julienrat/wemostowio/3D/wio_shield.png

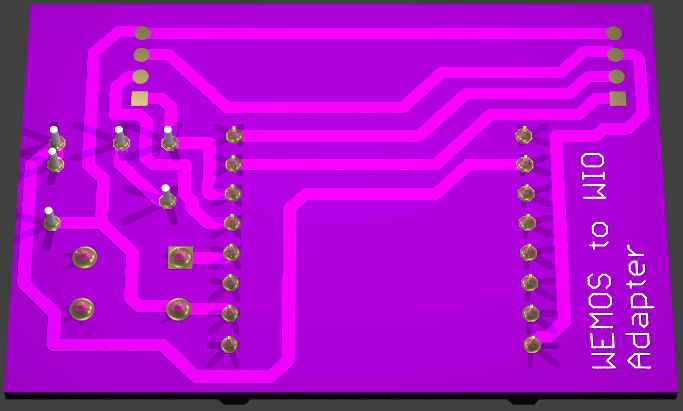
3D/wio_shield.png
