julienrat/wemostowio/3D/wio_shield_top.png

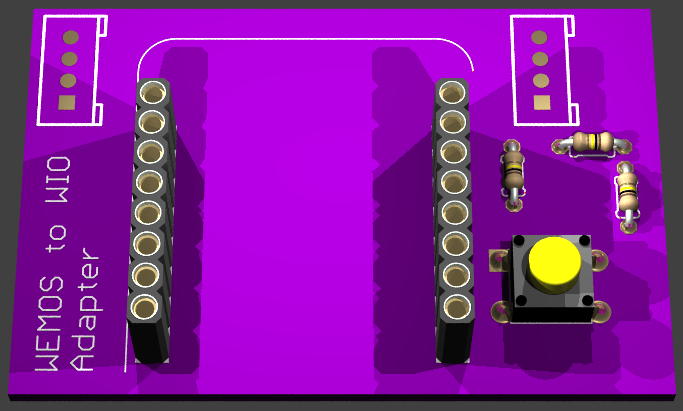
3D/wio_shield_top.png
