julienrat/wemostowio/images/PCB.png

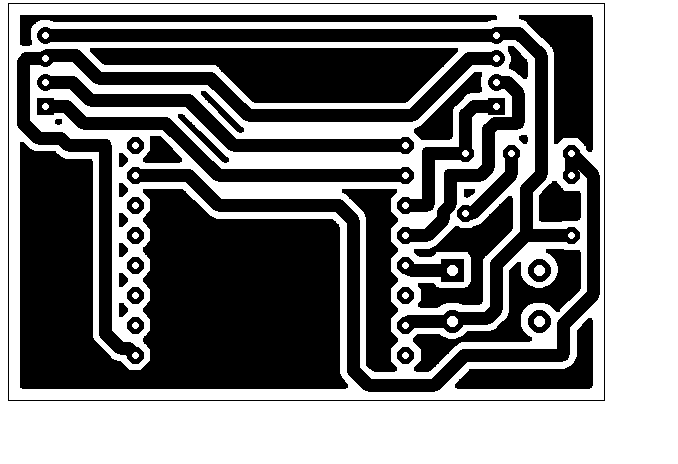
images/PCB.png
